TheRealFalseReality/aquapi/assets/STLModels/EZOCase/EZOBoard rev2.3mf

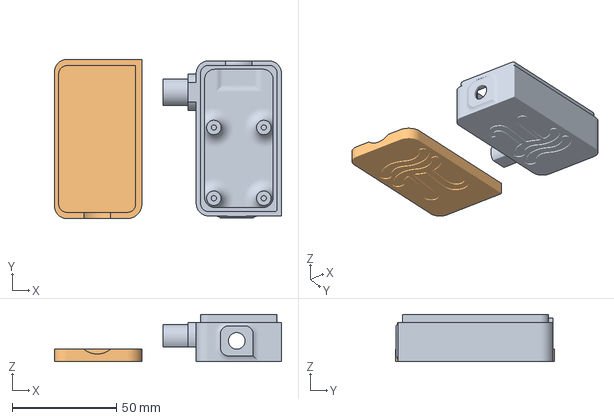
[picture p24: CAD file, 2026-02-03]
assets/STLModels/EZOCase/EZOBoard rev2.3mf
109.1 x 76.5 x 22.8 mm
EZOBoard Case rev2 v11.stl
EZOBoard Lid rev2 v14.stl
