TheRealFalseReality/aquapi/assets/STLModels/LeakSensor/Leak Sensor - Mag v13.stl

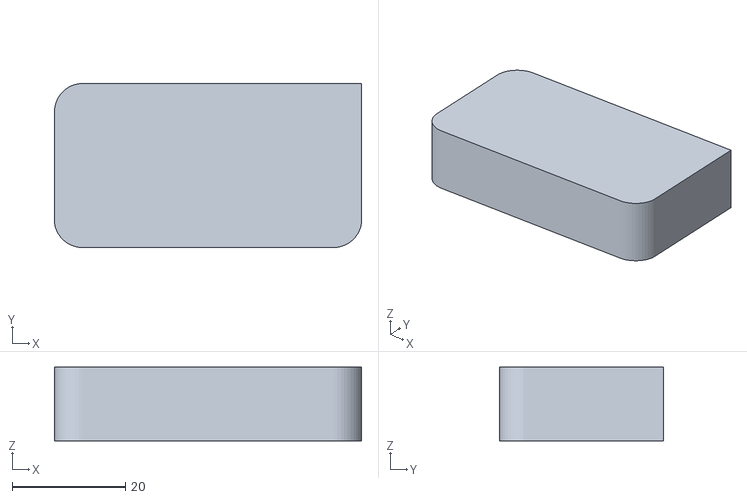
[picture p25: CAD file, 2025-01-13]
assets/STLModels/LeakSensor/Leak Sensor - Mag v13.stl
54.3 x 29.0 x 13.0
