TheRealFalseReality/aquapi/assets/STLModels/SnapCam/BallMount v9.stl

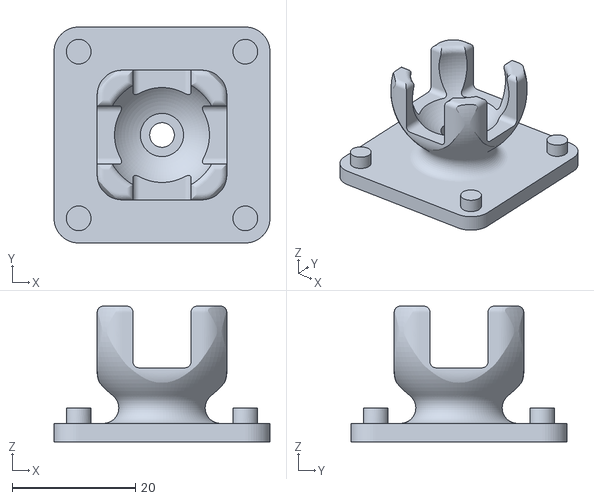
[picture p26: CAD file, 2024-07-31]
assets/STLModels/SnapCam/BallMount v9.stl
35.0 x 35.0 x 22.0
