TheRealFalseReality/aquapi/assets/STLModels/WaterLevelBracket/OpticalBracket_Holder.stl

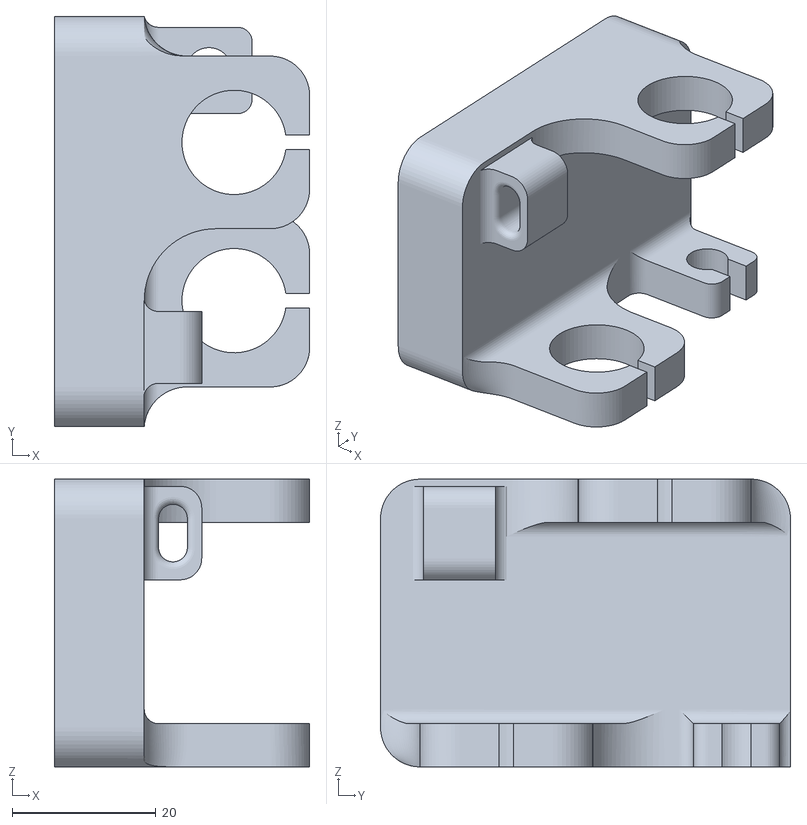
[picture p27: CAD file, 2026-02-03]
assets/STLModels/WaterLevelBracket/OpticalBracket_Holder.stl
35.5 x 57.0 x 40.0
