TheRealFalseReality/aquapi/assets/STLModels/AquaPiCase/AquaPi Case - Base v58.stl

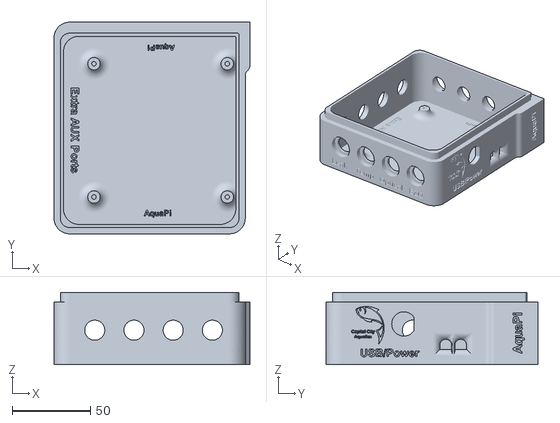
[picture p28: CAD file, 2026-02-03]
assets/STLModels/AquaPiCase/AquaPi Case - Base v58.stl
125.0 x 135.0 x 46.0
