TheRealFalseReality/aquapi/assets/STLModels/EZOPump/AquaPi Pump Lid - Red v26.stl

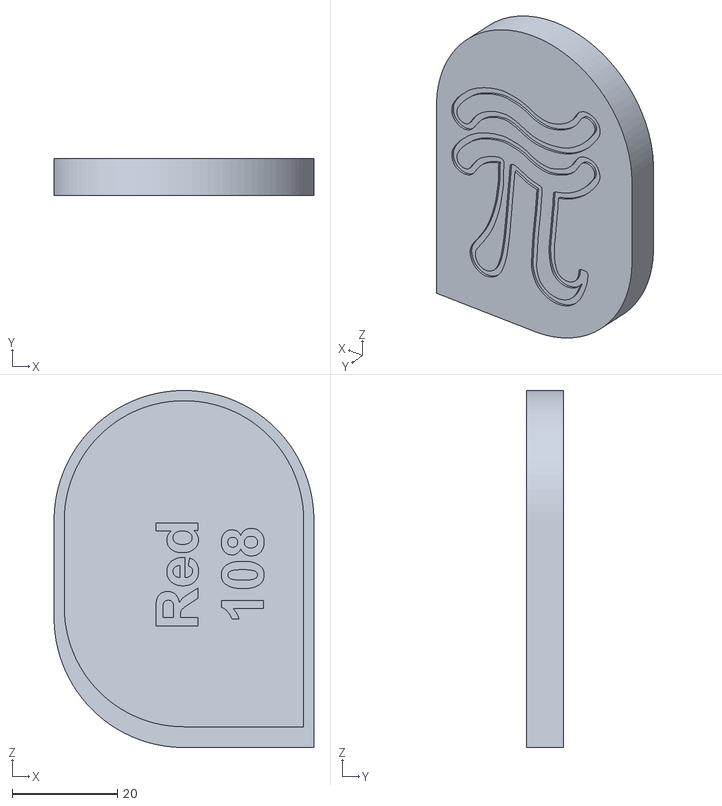
[picture p29: CAD file, 2026-02-03]
assets/STLModels/EZOPump/AquaPi Pump Lid - Red v26.stl
49.5 x 7.00 x 68.0
