TheRealFalseReality/aquapi/assets/STLModels/SnapCam/esp32Cam - Lid v32.stl

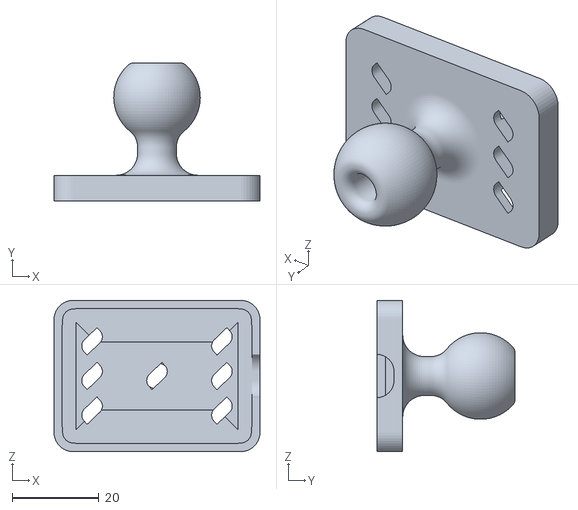
[picture p30: CAD file, 2024-07-31]
assets/STLModels/SnapCam/esp32Cam - Lid v32.stl
47.6 x 32.0 x 35.0
