TheRealFalseReality/aquapi/assets/STLModels/WaterLevelBracket/OpticalBracket Extender.stl

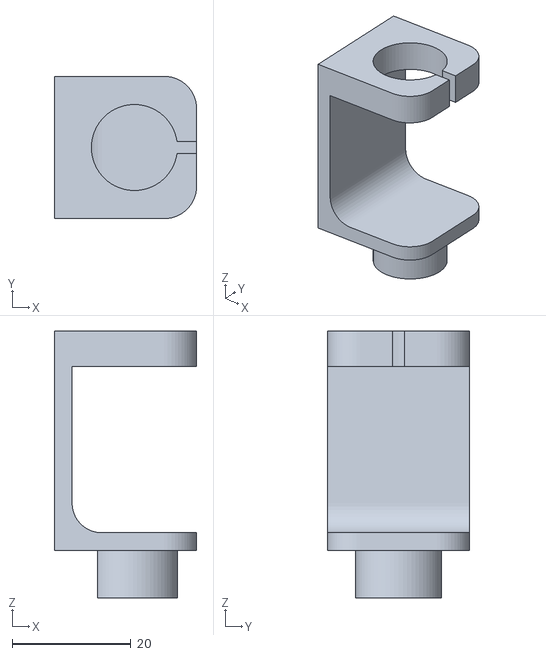
[picture p31: CAD file, 2025-01-13]
assets/STLModels/WaterLevelBracket/OpticalBracket Extender.stl
24.0 x 24.0 x 45.0
