TheRealFalseReality/aquapi/assets/STLModels/AquaPiCase/AquaPi Mount - Base v25.stl

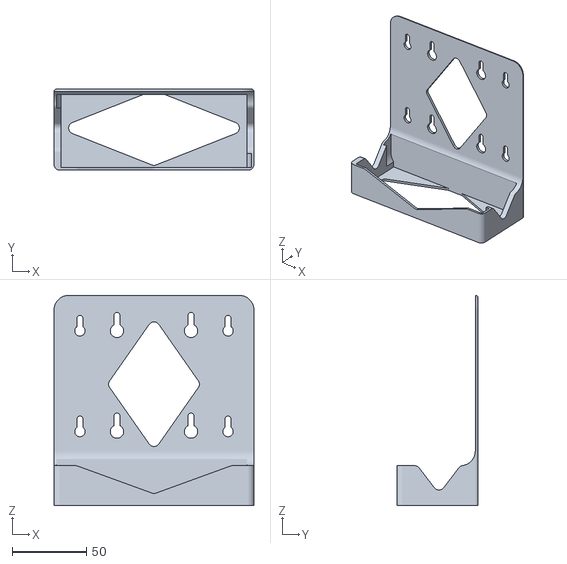
[picture p32: CAD file, 2024-11-28]
assets/STLModels/AquaPiCase/AquaPi Mount - Base v25.stl
135.0 x 55.0 x 142.0
