TheRealFalseReality/aquapi/assets/STLModels/AquaPiCase/AquaPi Mount - Hanger v25.stl

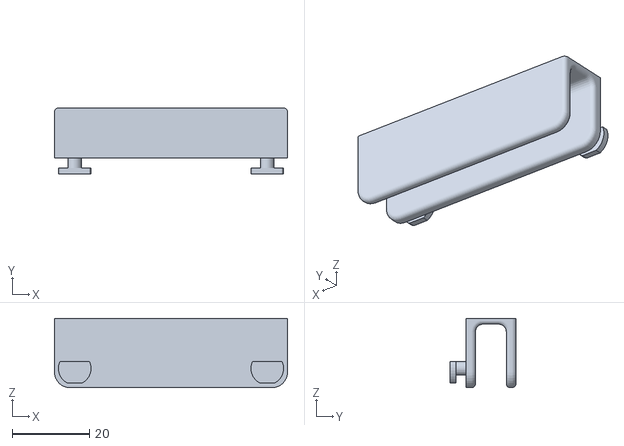
[picture p33: CAD file, 2024-11-28]
assets/STLModels/AquaPiCase/AquaPi Mount - Hanger v25.stl
60.5 x 17.1 x 18.0
