TheRealFalseReality/aquapi/assets/STLModels/AquaPiCase/AquaPi Case - Lid v45.stl

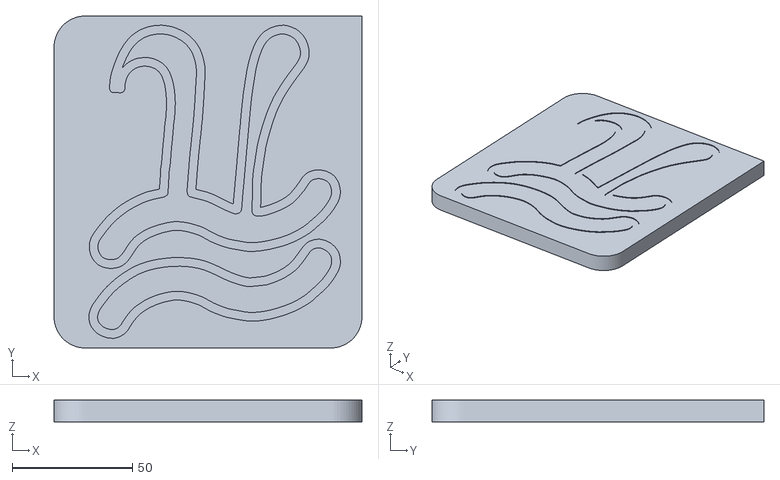
[picture p34: CAD file, 2024-07-30]
assets/STLModels/AquaPiCase/AquaPi Case - Lid v45.stl
128.0 x 138.0 x 9.00
