TheRealFalseReality/aquapi/common/ezo_pmp_duo.yaml

---
substitutions:
  # PMP circuit, who's address is 103
  addPMP_green: "109"  # Green - Clean
  addPMP_red: "108"  # Red - Waste #TODO Matches O2 sensor
  update_pmp_green: "60s"
  update_pmp_red: "60s"

  sorting_group_pump_green_weight: '81'
  sorting_group_pump_red_weight: '82'

web_server:
  sorting_groups:
    - id: sorting_group_pump_green
      name: "Pump - Green"
      sorting_weight: ${sorting_group_pump_green_weight}
    - id: sorting_group_pump_red
      name: "Pump - Red"
      sorting_weight: ${sorting_group_pump_red_weight}

ezo_pmp:
  - id: ezo_pump_green
    address: ${addPMP_green}
    update_interval: "${update_pmp_green}"
  - id: ezo_pump_red
    address: ${addPMP_red}
    update_interval: "${update_pmp_red}"

api:
  actions:
    - action: pump_waste_volume
      variables:
        dose_volume: float
      then:
        - ezo_pmp.dose_volume:
            id: ezo_pump_red
            volume: !lambda 'return dose_volume;'
    - action: pump_waste_volume_time
      variables:
        dose_volume: float
        dose_time: float
      then:
        - ezo_pmp.dose_volume_over_time:
            id: ezo_pump_red
            volume: !lambda |-
              return dose_volume;
            duration: !lambda |-
              return dose_time;
    - action: pump_waste_flow_rate_time
      variables:
        dose_rate: float
        dose_time: float
      then:
        - ezo_pmp.dose_with_constant_flow_rate:
            id: ezo_pump_red
            volume_per_minute: !lambda |-
              return dose_rate;
            duration: !lambda |-
              return dose_time;
    - action: pump_waste_set_calibration
      variables:
        actual_volume: float
      then:
        - ezo_pmp.set_calibration_volume:
            id: ezo_pump_red
            volume: !lambda |-
              return actual_volume;
    - action: pump_clean_volume
      variables:
        dose_volume: float
      then:
        - ezo_pmp.dose_volume:
            id: ezo_pump_green
            volume: !lambda 'return dose_volume;'
    - action: pump_clean_volume_time
      variables:
        dose_volume: float
        dose_time: float
      then:
        - ezo_pmp.dose_volume_over_time:
            id: ezo_pump_green
            volume: !lambda |-
              return dose_volume;
            duration: !lambda |-
              return dose_time;
    - action: pump_clean_flow_rate_time
      variables:
        dose_rate: float
        dose_time: float
      then:
        - ezo_pmp.dose_with_constant_flow_rate:
            id: ezo_pump_green
            volume_per_minute: !lambda |-
              return dose_rate;
            duration: !lambda |-
              return dose_time;
    - action: pump_clean_set_calibration
      variables:
        actual_volume: float
      then:
        - ezo_pmp.set_calibration_volume:
            id: ezo_pump_green
            volume: !lambda |-
              return actual_volume;
    - action: pump_water_change
      variables:
        volume: float
        duration: float
      then:
        - ezo_pmp.dose_volume_over_time:
            id: ezo_pump_green
            volume: !lambda |-
              return volume;
            duration: !lambda |-
              return duration;
        - ezo_pmp.dose_volume_over_time:
            id: ezo_pump_red
            volume: !lambda |-
              return volume;
            duration: !lambda |-
              return duration;
    - action: pump_water_change_quick
      variables:
        volume: float
      then:
        - ezo_pmp.dose_volume:
            id: ezo_pump_green
            volume: !lambda |-
              return volume;
        - ezo_pmp.dose_volume:
            id: ezo_pump_red
            volume: !lambda |-
              return volume;
    - action: pump_waste_change_address
      variables:
        address: int
      then:
        - ezo_pmp.change_i2c_address:
            id: ezo_pump_red
            address: !lambda |-
              return address;
    - action: pump_clean_change_address
      variables:
        address: int
      then:
        - ezo_pmp.change_i2c_address:
            id: ezo_pump_green
            address: !lambda |-
              return address;

sensor:
  # Green
  - platform: ezo_pmp
    id: ezo_pump_green
    current_volume_dosed:
      id: current_volume_dosed_clean
      name: Pump Clean - Current Volume Dosed
      disabled_by_default: true
      icon: mdi:cube-scan
      device_class: 'volume'
      state_class: total
      unit_of_measurement: 'mL'
      web_server:
        sorting_group_id: sorting_group_pump_green
  - platform: ezo_pmp
    id: ezo_pump_green
    total_volume_dosed:
      id: total_volume_dosed_clean
      name: Pump Clean - Total Volume Dosed
      icon: mdi:timer-sand-empty
      disabled_by_default: true
      device_class: 'volume'
      unit_of_measurement: 'mL'
      web_server:
        sorting_group_id: sorting_group_pump_green
  - platform: ezo_pmp
    id: ezo_pump_green
    absolute_total_volume_dosed:
      id: absolute_total_volume_dosed_clean
      name: Pump Clean - Absolute Total Volume Dosed
      icon: mdi:timer-sand-full
      device_class: 'volume'
      state_class: total
      unit_of_measurement: 'mL'
      disabled_by_default: true
      web_server:
        sorting_group_id: sorting_group_pump_green
  - platform: ezo_pmp
    id: ezo_pump_green
    last_volume_requested:
      id: last_volume_requested_clean
      name: Pump Clean - Last Volume Requested
      icon: mdi:history
      device_class: 'volume'
      state_class: total
      unit_of_measurement: 'mL'
      disabled_by_default: true
      web_server:
        sorting_group_id: sorting_group_pump_green
  - platform: ezo_pmp
    id: ezo_pump_green
    max_flow_rate:
      id: max_flow_rate_clean
      name: Pump Clean - Max Volume-Time Flow Rate
      icon: mdi:car-speed-limiter
      unit_of_measurement: 'mL/min'
      disabled_by_default: true
      web_server:
        sorting_group_id: sorting_group_pump_green
  - platform: ezo_pmp
    id: ezo_pump_green
    pump_voltage:
      id: pump_voltage_clean
      name: Pump Clean - Voltage
      icon: mdi:lightning-bolt-circle
      disabled_by_default: true
      device_class: 'voltage'
      web_server:
        sorting_group_id: sorting_group_pump_green

  # Red
  - platform: ezo_pmp
    id: ezo_pump_red
    current_volume_dosed:
      id: current_volume_dosed_waste
      name: Pump Waste - Current Volume Dosed
      disabled_by_default: true
      icon: mdi:cube-scan
      device_class: 'volume'
      state_class: total
      unit_of_measurement: 'mL'
      web_server:
        sorting_group_id: sorting_group_pump_red
  - platform: ezo_pmp
    id: ezo_pump_red
    total_volume_dosed:
      id: total_volume_dosed_waste
      name: Pump Waste - Total Volume Dosed
      icon: mdi:timer-sand-empty
      device_class: 'volume'
      unit_of_measurement: 'mL'
      disabled_by_default: true
      web_server:
        sorting_group_id: sorting_group_pump_red
  - platform: ezo_pmp
    id: ezo_pump_red
    absolute_total_volume_dosed:
      id: absolute_total_volume_dosed_waste
      name: Pump Waste - Absolute Total Volume Dosed
      icon: mdi:timer-sand-full
      device_class: 'volume'
      state_class: total
      disabled_by_default: true
      unit_of_measurement: 'mL'
      web_server:
        sorting_group_id: sorting_group_pump_red
  - platform: ezo_pmp
    id: ezo_pump_red
    last_volume_requested:
      id: last_volume_requested_waste
      name: Pump Waste - Last Volume Requested
      icon: mdi:history
      state_class: total
      device_class: 'volume'
      unit_of_measurement: 'mL'
      disabled_by_default: true
      web_server:
        sorting_group_id: sorting_group_pump_red
  - platform: ezo_pmp
    id: ezo_pump_red
    max_flow_rate:
      id: max_flow_rate_waste
      name: Pump Waste - Max Volume-Time Flow Rate
      icon: mdi:car-speed-limiter
      unit_of_measurement: 'mL/min'
      disabled_by_default: true
      web_server:
        sorting_group_id: sorting_group_pump_red
  - platform: ezo_pmp
    id: ezo_pump_red
    pump_voltage:
      id: pump_voltage_waste
      name: Pump Waste - Voltage
      icon: mdi:lightning-bolt-circle
      disabled_by_default: true
      device_class: 'voltage'
      web_server:
        sorting_group_id: sorting_group_pump_red

binary_sensor:
  # Green
  - platform: ezo_pmp
    id: ezo_pump_green
    pump_state:
      id: pump_state_clean
      icon: mdi:pump
      name: Pump Clean - State
      disabled_by_default: true
      web_server:
        sorting_group_id: sorting_group_pump_green
  - platform: ezo_pmp
    id: ezo_pump_green
    is_paused:
      id: is_paused_clean
      name: Pump Clean - Paused Status
      icon: mdi:pause
      disabled_by_default: true
      web_server:
        sorting_group_id: sorting_group_pump_green

  # Red
  - platform: ezo_pmp
    id: ezo_pump_red
    pump_state:
      id: pump_state_waste
      icon: mdi:pump
      name: Pump Waste - State
      disabled_by_default: true
      web_server:
        sorting_group_id: sorting_group_pump_red
  - platform: ezo_pmp
    id: ezo_pump_red
    is_paused:
      id: is_paused_waste
      name: Pump Waste - Paused Status
      icon: mdi:pause
      disabled_by_default: true
      web_server:
        sorting_group_id: sorting_group_pump_red

text_sensor:
  # Green
  - platform: ezo_pmp
    id: ezo_pump_green
    dosing_mode:
      id: dosing_mode_clean
      name: Pump Clean - Dosing Mode
      disabled_by_default: true
      icon: mdi:auto-mode
      web_server:
        sorting_group_id: sorting_group_pump_green
  - platform: ezo_pmp
    id: ezo_pump_green
    calibration_status:
      id: calibration_status_clean
      name: Pump Clean - Calibration Status
      disabled_by_default: true
      icon: mdi:tape-measure
      web_server:
        sorting_group_id: sorting_group_pump_green

  # Red
  - platform: ezo_pmp
    id: ezo_pump_red
    dosing_mode:
      id: dosing_mode_waste
      name: Pump Waste - Dosing Mode
      disabled_by_default: true
      icon: mdi:auto-mode
      web_server:
        sorting_group_id: sorting_group_pump_red
  - platform: ezo_pmp
    id: ezo_pump_red
    calibration_status:
      id: calibration_status_waste
      name: Pump Waste - Calibration Status
      disabled_by_default: true
      icon: mdi:tape-measure
      web_server:
        sorting_group_id: sorting_group_pump_red

number:
  # Green
  - platform: template
    id: volume_clean
    icon: mdi:pump
    name: Pump Clean - Volume to Dose (negative = reverse)
    disabled_by_default: true
    device_class: 'volume'
    unit_of_measurement: 'mL'
    optimistic: true
    initial_value: 10  # cannot be less than +/-0.1mL
    min_value: -378541  # Negative values run pump in reverse direction
    max_value: 378541   # 100 gal in mL
    mode: box
    step: 0.1
    web_server:
      sorting_group_id: sorting_group_pump_green
  - platform: template
    id: duration_clean
    icon: mdi:timer
    name: Pump Clean - Time to Dose
    disabled_by_default: true
    device_class: 'duration'
    unit_of_measurement: 'min'
    optimistic: true
    initial_value: 1
    min_value: 1
    max_value: 1440  # 24 hours
    mode: box
    step: 0.1
    web_server:
      sorting_group_id: sorting_group_pump_green
  - platform: template
    id: flow_rate_clean
    icon: mdi:waves-arrow-right
    name: Pump Clean - Volume-Time Flow Rate
    disabled_by_default: true
    unit_of_measurement: 'mL/min'
    optimistic: true
    initial_value: 10
    min_value: .5
    max_value: 105  # may need to lower to 40
    mode: box
    step: 0.1
    web_server:
      sorting_group_id: sorting_group_pump_green

  # Red
  - platform: template
    id: volume_waste
    icon: mdi:pump
    name: Pump Waste - Volume to Dose (negative = reverse)
    disabled_by_default: true
    device_class: 'volume'
    unit_of_measurement: 'mL'
    optimistic: true
    initial_value: 10  # cannot be less than +/-0.1mL
    min_value: -378541  # Negative values run pump in reverse direction
    max_value: 378541   # 100 gal in mL
    mode: box
    step: 0.1
    web_server:
      sorting_group_id: sorting_group_pump_red
  - platform: template
    id: duration_waste
    icon: mdi:timer
    name: Pump Waste - Time to Dose
    disabled_by_default: true
    device_class: 'duration'
    unit_of_measurement: 'min'
    optimistic: true
    initial_value: 1
    min_value: 1
    max_value: 1440  # 24 hours
    mode: box
    step: 0.1
    web_server:
      sorting_group_id: sorting_group_pump_red
  - platform: template
    id: flow_rate_waste
    icon: mdi:waves-arrow-left
    name: Pump Waste - Volume-Time Flow Rate
    disabled_by_default: true
    unit_of_measurement: 'mL/min'
    optimistic: true
    initial_value: 10
    min_value: .5
    max_value: 105  # may need to lower to 40
    mode: box
    step: 0.1
    web_server:
      sorting_group_id: sorting_group_pump_red

button:
  # Green
  - platform: template
    name: Pump Clean - Dose Volume for Time
    disabled_by_default: true
    icon: mdi:clock-time-two-outline
    id: dose_over_time_clean
    on_press:
      - ezo_pmp.dose_volume_over_time:
          id: ezo_pump_green
          volume: !lambda |-
            return id(volume_clean).state;
          duration: !lambda |-
            return id(duration_clean).state;
    web_server:
      sorting_group_id: sorting_group_pump_green
  - platform: template
    name: Pump Clean - Dose Continuously
    disabled_by_default: true
    icon: mdi:infinity
    id: dose_continuously_clean
    on_press:
      - ezo_pmp.dose_continuously:
          id: ezo_pump_green
    web_server:
      sorting_group_id: sorting_group_pump_green
  - platform: template
    name: Pump Clean - Dose Volume (negative = reverse)
    disabled_by_default: true
    icon: mdi:pump
    id: dose_volume_clean
    on_press:
      - ezo_pmp.dose_volume:
          id: ezo_pump_green
          volume: !lambda |-
            return id(volume_clean).state;
    web_server:
      sorting_group_id: sorting_group_pump_green
  - platform: template
    name: Pump Clean - Dose at Volume-Time Flow Rate for Time
    disabled_by_default: true
    icon: mdi:format-text-wrapping-overflow
    id: dose_flow_rate_clean
    on_press:
      - ezo_pmp.dose_with_constant_flow_rate:
          id: ezo_pump_green
          volume_per_minute: !lambda |-
            return id(flow_rate_clean).state;
          duration: !lambda |-
            return id(duration_clean).state;
    web_server:
      sorting_group_id: sorting_group_pump_green
  - platform: template
    name: Pump Clean - Pause Dosing
    disabled_by_default: true
    icon: mdi:pause
    id: dose_pause_clean
    on_press:
      - ezo_pmp.pause_dosing:
          id: ezo_pump_green
    web_server:
      sorting_group_id: sorting_group_pump_green
  - platform: template
    name: Pump Clean - Stop Dosing
    disabled_by_default: true
    icon: mdi:stop
    id: dose_stop_clean
    on_press:
      - ezo_pmp.stop_dosing:
          id: ezo_pump_green
    web_server:
      sorting_group_id: sorting_group_pump_green
  - platform: template
    name: Pump Clean - Clear Total Volume Dosed
    disabled_by_default: true
    icon: mdi:backspace
    id: dose_clear_clean
    on_press:
      - ezo_pmp.clear_total_volume_dosed:
          id: ezo_pump_green
    web_server:
      sorting_group_id: sorting_group_pump_green
  - platform: template
    name: Pump Clean - Set Calibration Volume
    disabled_by_default: true
    icon: mdi:tape-measure
    id: dose_calibrate_volume_clean
    on_press:
      - ezo_pmp.set_calibration_volume:
          id: ezo_pump_green
          volume: !lambda |-
            return id(volume_clean).state;
    web_server:
      sorting_group_id: sorting_group_pump_green
  - platform: template
    name: Pump Clean - Clear Calibration Volume
    icon: mdi:cancel
    id: dose_calibrate_volume_clear_clean
    disabled_by_default: true
    on_press:
      - ezo_pmp.clear_calibration:
          id: ezo_pump_green
    web_server:
      sorting_group_id: sorting_group_pump_green

  # Red
  - platform: template
    name: Pump Waste - Dose Volume for Time
    disabled_by_default: true
    icon: mdi:clock-time-two-outline
    id: dose_over_time_waste
    on_press:
      - ezo_pmp.dose_volume_over_time:
          id: ezo_pump_red
          volume: !lambda |-
            return id(volume_waste).state;
          duration: !lambda |-
            return id(duration_waste).state;
    web_server:
      sorting_group_id: sorting_group_pump_red
  - platform: template
    name: Pump Waste - Dose Continuously
    disabled_by_default: true
    icon: mdi:infinity
    id: dose_continuously_waste
    on_press:
      - ezo_pmp.dose_continuously:
          id: ezo_pump_red
    web_server:
      sorting_group_id: sorting_group_pump_red
  - platform: template
    name: Pump Waste - Dose Volume (negative = reverse)
    disabled_by_default: true
    icon: mdi:pump
    id: dose_volume_waste
    on_press:
      - ezo_pmp.dose_volume:
          id: ezo_pump_red
          volume: !lambda |-
            return id(volume_waste).state;
    web_server:
      sorting_group_id: sorting_group_pump_red
  - platform: template
    name: Pump Waste - Dose at Volume-Time Flow Rate for Time
    disabled_by_default: true
    icon: mdi:format-text-wrapping-overflow
    id: dose_flow_rate_waste
    on_press:
      - ezo_pmp.dose_with_constant_flow_rate:
          id: ezo_pump_red
          volume_per_minute: !lambda |-
            return id(flow_rate_waste).state;
          duration: !lambda |-
            return id(duration_waste).state;
    web_server:
      sorting_group_id: sorting_group_pump_red
  - platform: template
    name: Pump Waste - Pause Dosing
    disabled_by_default: true
    icon: mdi:pause
    id: dose_pause_waste
    on_press:
      - ezo_pmp.pause_dosing:
          id: ezo_pump_red
    web_server:
      sorting_group_id: sorting_group_pump_red
  - platform: template
    name: Pump Waste - Stop Dosing
    disabled_by_default: true
    icon: mdi:stop
    id: dose_stop_waste
    on_press:
      - ezo_pmp.stop_dosing:
          id: ezo_pump_red
    web_server:
      sorting_group_id: sorting_group_pump_red
  - platform: template
    name: Pump Waste - Clear Total Volume Dosed
    icon: mdi:backspace
    disabled_by_default: true
    id: dose_clear_waste
    on_press:
      - ezo_pmp.clear_total_volume_dosed:
          id: ezo_pump_red
    web_server:
      sorting_group_id: sorting_group_pump_red
  - platform: template
    name: Pump Waste - Set Calibration Volume
    disabled_by_default: true
    icon: mdi:tape-measure
    id: dose_calibrate_volume_waste
    on_press:
      - ezo_pmp.set_calibration_volume:
          id: ezo_pump_red
          volume: !lambda |-
            return id(volume_waste).state;
    web_server:
      sorting_group_id: sorting_group_pump_red
  - platform: template
    name: Pump Waste - Clear Calibration Volume
    disabled_by_default: true
    icon: mdi:cancel
    id: dose_calibrate_volume_clear_waste
    on_press:
      - ezo_pmp.clear_calibration:
          id: ezo_pump_red
    web_server:
      sorting_group_id: sorting_group_pump_red
