TheRealFalseReality/aquapi/common/ezo_pmp_blue.yaml

---
substitutions:
  # PMP circuit
  addPMP_blue: "106"  # blue
  update_pmp_blue: "60s"
  sorting_group_pump_blue_weight: '83'

web_server:
  sorting_groups:
    - id: sorting_group_pump_blue
      name: "Pump - Blue"
      sorting_weight: ${sorting_group_pump_blue_weight}

ezo_pmp:
  - id: ezo_pump_blue
    address: ${addPMP_blue}
    update_interval: "${update_pmp_blue}"

api:
  actions:
    - action: pump_blue_dose_volume
      variables:
        dose_volume: float
      then:
        - ezo_pmp.dose_volume:
            id: ezo_pump_blue
            volume: !lambda 'return dose_volume;'
    - action: pump_blue_dose_volume_time
      variables:
        dose_volume: float
        dose_time: float
      then:
        - ezo_pmp.dose_volume_over_time:
            id: ezo_pump_blue
            volume: !lambda |-
              return dose_volume;
            duration: !lambda |-
              return dose_time;
    - action: pump_blue_dose_flow_rate_time
      variables:
        dose_rate: float
        dose_time: float
      then:
        - ezo_pmp.dose_with_constant_flow_rate:
            id: ezo_pump_blue
            volume_per_minute: !lambda |-
              return dose_rate;
            duration: !lambda |-
              return dose_time;
    - action: pump_blue_dose_set_calibration
      variables:
        actual_volume: float
      then:
        - ezo_pmp.set_calibration_volume:
            id: ezo_pump_blue
            volume: !lambda |-
              return actual_volume;
    - action: pump_blue_change_address
      variables:
        address: int
      then:
        - ezo_pmp.change_i2c_address:
            id: ezo_pump_blue
            address: !lambda |-
              return address;

sensor:
  - platform: ezo_pmp
    id: ezo_pump_blue
    current_volume_dosed:
      id: current_volume_dosed_blue
      name: Pump Blue - Current Volume Dosed
      icon: mdi:cube-scan
      device_class: 'volume'
      state_class: total
      unit_of_measurement: 'mL'
      web_server:
        sorting_group_id: sorting_group_pump_blue
  - platform: ezo_pmp
    id: ezo_pump_blue
    total_volume_dosed:
      id: total_volume_dosed_blue
      name: Pump Blue - Total Volume Dosed
      icon: mdi:timer-sand-empty
      device_class: 'volume'
      unit_of_measurement: 'mL'
      disabled_by_default: true
      web_server:
        sorting_group_id: sorting_group_pump_blue
  - platform: ezo_pmp
    id: ezo_pump_blue
    absolute_total_volume_dosed:
      id: absolute_total_volume_dosed_blue
      name: Pump Blue - Absolute Total Volume Dosed
      icon: mdi:timer-sand-full
      disabled_by_default: true
      device_class: 'volume'
      state_class: total
      unit_of_measurement: 'mL'
      web_server:
        sorting_group_id: sorting_group_pump_blue
  - platform: ezo_pmp
    id: ezo_pump_blue
    last_volume_requested:
      id: last_volume_requested_blue
      name: Pump Blue - Last Volume Requested
      icon: mdi:history
      device_class: 'volume'
      disabled_by_default: true
      state_class: total
      unit_of_measurement: 'mL'
      web_server:
        sorting_group_id: sorting_group_pump_blue
  - platform: ezo_pmp
    id: ezo_pump_blue
    max_flow_rate:
      id: max_flow_rate_blue
      name: Pump Blue - Max Volume-Time Flow Rate
      icon: mdi:car-speed-limiter
      disabled_by_default: true
      unit_of_measurement: 'mL/min'
      web_server:
        sorting_group_id: sorting_group_pump_blue
  - platform: ezo_pmp
    id: ezo_pump_blue
    pump_voltage:
      id: pump_blue_voltage
      name: Pump Blue - Voltage
      disabled_by_default: true
      icon: mdi:lightning-bolt-circle
      device_class: 'voltage'
      web_server:
        sorting_group_id: sorting_group_pump_blue

binary_sensor:
  - platform: ezo_pmp
    id: ezo_pump_blue
    pump_state:
      id: pump_blue_state
      name: Pump Blue - State
      icon: mdi:pump_blue
  - platform: ezo_pmp
    id: ezo_pump_blue
    is_paused:
      id: is_paused_blue
      name: Pump Blue - Paused Status
      icon: mdi:pause
      disabled_by_default: true
      web_server:
        sorting_group_id: sorting_group_pump_blue

text_sensor:
  - platform: ezo_pmp
    id: ezo_pump_blue
    dosing_mode:
      id: dosing_mode_blue
      name: Pump Blue - Dosing Mode
      icon: mdi:auto-mode
      web_server:
        sorting_group_id: sorting_group_pump_blue
  - platform: ezo_pmp
    id: ezo_pump_blue
    calibration_status:
      id: calibration_status_blue
      name: Pump Blue - Calibration Status
      disabled_by_default: true
      icon: mdi:tape-measure
      web_server:
        sorting_group_id: sorting_group_pump_blue

number:
  - platform: template
    id: volume_blue
    icon: mdi:pump_blue
    name: Pump Blue - Volume to Dose (negative = reverse)
    device_class: 'volume'
    unit_of_measurement: 'mL'
    optimistic: true
    initial_value: 10  # cannot be less than +/-0.1mL
    min_value: -378541  # Negative values run pump in reverse direction
    max_value: 378541   # 100 gal in mL
    mode: box
    step: 0.1
    web_server:
      sorting_group_id: sorting_group_pump_blue
  - platform: template
    id: duration_blue
    icon: mdi:timer
    name: Pump Blue - Time to Dose
    device_class: 'duration'
    unit_of_measurement: 'min'
    optimistic: true
    initial_value: 1
    min_value: 1
    max_value: 1440  # 24 hours
    mode: box
    step: 0.1
    web_server:
      sorting_group_id: sorting_group_pump_blue
  - platform: template
    id: flow_rate_blue
    icon: mdi:waves-arrow-right
    name: Pump Blue - Volume-Time Flow Rate
    unit_of_measurement: 'mL/min'
    optimistic: true
    initial_value: 10
    min_value: .5
    max_value: 105  # may need to lower to 40
    mode: box
    step: 0.1
    web_server:
      sorting_group_id: sorting_group_pump_blue

button:
  - platform: template
    name: Pump Blue - Dose Volume for Time
    icon: mdi:clock-time-two-outline
    id: dose_over_time_blue
    on_press:
      - ezo_pmp.dose_volume_over_time:
          id: ezo_pump_blue
          volume: !lambda |-
            return id(volume_blue).state;
          duration: !lambda |-
            return id(volume_blue).state;
    web_server:
      sorting_group_id: sorting_group_pump_blue
  - platform: template
    name: Pump Blue - Dose Continuously
    icon: mdi:infinity
    id: dose_continuously_blue
    on_press:
      - ezo_pmp.dose_continuously:
          id: ezo_pump_blue
    web_server:
      sorting_group_id: sorting_group_pump_blue
  - platform: template
    name: Pump Blue - Dose Volume (negative = reverse)
    icon: mdi:pump_blue
    id: dose_volume_blue
    on_press:
      - ezo_pmp.dose_volume:
          id: ezo_pump_blue
          volume: !lambda |-
            return id(volume_blue).state;
    web_server:
      sorting_group_id: sorting_group_pump_blue
  - platform: template
    name: Pump Blue - Dose at Volume-Time Flow Rate for Time
    icon: mdi:format-text-wrapping-overflow
    id: dose_flow_rate_blue
    on_press:
      - ezo_pmp.dose_with_constant_flow_rate:
          id: ezo_pump_blue
          volume_per_minute: !lambda |-
            return id(volume_blue).state;
          duration: !lambda |-
            return id(volume_blue).state;
    web_server:
      sorting_group_id: sorting_group_pump_blue
  - platform: template
    name: Pump Blue - Pause Dosing
    icon: mdi:pause
    id: dose_pause_blue
    on_press:
      - ezo_pmp.pause_dosing:
          id: ezo_pump_blue
    web_server:
      sorting_group_id: sorting_group_pump_blue
  - platform: template
    name: Pump Blue - Stop Dosing
    icon: mdi:stop
    id: dose_stop_blue
    on_press:
      - ezo_pmp.stop_dosing:
          id: ezo_pump_blue
    web_server:
      sorting_group_id: sorting_group_pump_blue
  - platform: template
    name: Pump Blue - Clear Total Volume Dosed
    disabled_by_default: true
    icon: mdi:backspace
    id: dose_clear_blue
    on_press:
      - ezo_pmp.clear_total_volume_dosed:
          id: ezo_pump_blue
    web_server:
      sorting_group_id: sorting_group_pump_blue

  # Calibrate
  - platform: template
    name: Pump Blue - Set Calibration Volume
    icon: mdi:tape-measure
    id: dose_calibrate_volume_blue
    on_press:
      - ezo_pmp.set_calibration_volume:
          id: ezo_pump_blue
          volume: !lambda |-
            return id(volume_blue).state;
    web_server:
      sorting_group_id: sorting_group_pump_blue
  - platform: template
    name: Pump Blue - Clear Calibration Volume
    disabled_by_default: true
    icon: mdi:cancel
    id: dose_calibrate_volume_clear_blue
    on_press:
      - ezo_pmp.clear_calibration:
          id: ezo_pump_blue
    web_server:
      sorting_group_id: sorting_group_pump_blue
