TheRealFalseReality/aquapi/common/ezo_pmp_yellow.yaml

---
substitutions:
  # PMP circuit
  addPMP_yellow: "104"  # Yellow
  update_pmp_yellow: "60s"
  sorting_group_pump_yellow_weight: '85'

web_server:
  sorting_groups:
    - id: sorting_group_pump_yellow
      name: "Pump - Yellow"
      sorting_weight: ${sorting_group_pump_yellow_weight}

ezo_pmp:
  - id: ezo_pump_yellow
    address: ${addPMP_yellow}
    update_interval: "${update_pmp_yellow}"

api:
  actions:
    - action: pump_yellow_dose_volume
      variables:
        dose_volume: float
      then:
        - ezo_pmp.dose_volume:
            id: ezo_pump_yellow
            volume: !lambda 'return dose_volume;'
    - action: pump_yellow_dose_volume_time
      variables:
        dose_volume: float
        dose_time: float
      then:
        - ezo_pmp.dose_volume_over_time:
            id: ezo_pump_yellow
            volume: !lambda |-
              return dose_volume;
            duration: !lambda |-
              return dose_time;
    - action: pump_yellow_dose_flow_rate_time
      variables:
        dose_rate: float
        dose_time: float
      then:
        - ezo_pmp.dose_with_constant_flow_rate:
            id: ezo_pump_yellow
            volume_per_minute: !lambda |-
              return dose_rate;
            duration: !lambda |-
              return dose_time;
    - action: pump_yellow_dose_set_calibration
      variables:
        actual_volume: float
      then:
        - ezo_pmp.set_calibration_volume:
            id: ezo_pump_yellow
            volume: !lambda |-
              return actual_volume;
    - action: pump_yellow_change_address
      variables:
        address: int
      then:
        - ezo_pmp.change_i2c_address:
            id: ezo_pump_yellow
            address: !lambda |-
              return address;

sensor:
  - platform: ezo_pmp
    id: ezo_pump_yellow
    current_volume_dosed:
      id: current_volume_dosed_yellow
      name: Pump Yellow - Current Volume Dosed
      icon: mdi:cube-scan
      device_class: 'volume'
      state_class: total
      unit_of_measurement: 'mL'
      web_server:
        sorting_group_id: sorting_group_pump_yellow
  - platform: ezo_pmp
    id: ezo_pump_yellow
    total_volume_dosed:
      id: total_volume_dosed_yellow
      name: Pump Yellow - Total Volume Dosed
      icon: mdi:timer-sand-empty
      device_class: 'volume'
      unit_of_measurement: 'mL'
      disabled_by_default: true
      web_server:
        sorting_group_id: sorting_group_pump_yellow
  - platform: ezo_pmp
    id: ezo_pump_yellow
    absolute_total_volume_dosed:
      id: absolute_total_volume_dosed_yellow
      name: Pump Yellow - Absolute Total Volume Dosed
      icon: mdi:timer-sand-full
      disabled_by_default: true
      device_class: 'volume'
      state_class: total
      unit_of_measurement: 'mL'
      web_server:
        sorting_group_id: sorting_group_pump_yellow
  - platform: ezo_pmp
    id: ezo_pump_yellow
    last_volume_requested:
      id: last_volume_requested_yellow
      name: Pump Yellow - Last Volume Requested
      icon: mdi:history
      device_class: 'volume'
      disabled_by_default: true
      state_class: total
      unit_of_measurement: 'mL'
      web_server:
        sorting_group_id: sorting_group_pump_yellow
  - platform: ezo_pmp
    id: ezo_pump_yellow
    max_flow_rate:
      id: max_flow_rate_yellow
      name: Pump Yellow - Max Volume-Time Flow Rate
      icon: mdi:car-speed-limiter
      disabled_by_default: true
      unit_of_measurement: 'mL/min'
      web_server:
        sorting_group_id: sorting_group_pump_yellow
  - platform: ezo_pmp
    id: ezo_pump_yellow
    pump_voltage:
      id: pump_yellow_voltage
      name: Pump Yellow - Voltage
      disabled_by_default: true
      icon: mdi:lightning-bolt-circle
      device_class: 'voltage'
      web_server:
        sorting_group_id: sorting_group_pump_yellow

binary_sensor:
  - platform: ezo_pmp
    id: ezo_pump_yellow
    pump_state:
      id: pump_yellow_state
      name: Pump Yellow - State
      icon: mdi:pump_yellow
  - platform: ezo_pmp
    id: ezo_pump_yellow
    is_paused:
      id: is_paused_yellow
      name: Pump Yellow - Paused Status
      icon: mdi:pause
      disabled_by_default: true
      web_server:
        sorting_group_id: sorting_group_pump_yellow

text_sensor:
  - platform: ezo_pmp
    id: ezo_pump_yellow
    dosing_mode:
      id: dosing_mode_yellow
      name: Pump Yellow - Dosing Mode
      icon: mdi:auto-mode
      web_server:
        sorting_group_id: sorting_group_pump_yellow
  - platform: ezo_pmp
    id: ezo_pump_yellow
    calibration_status:
      id: calibration_status_yellow
      name: Pump Yellow - Calibration Status
      disabled_by_default: true
      icon: mdi:tape-measure
      web_server:
        sorting_group_id: sorting_group_pump_yellow

number:
  - platform: template
    id: volume_yellow
    icon: mdi:pump_yellow
    name: Pump Yellow - Volume to Dose (negative = reverse)
    device_class: 'volume'
    unit_of_measurement: 'mL'
    optimistic: true
    initial_value: 10  # cannot be less than +/-0.1mL
    min_value: -378541  # Negative values run pump in reverse direction
    max_value: 378541   # 100 gal in mL
    mode: box
    step: 0.1
    web_server:
      sorting_group_id: sorting_group_pump_yellow
  - platform: template
    id: duration_yellow
    icon: mdi:timer
    name: Pump Yellow - Time to Dose
    device_class: 'duration'
    unit_of_measurement: 'min'
    optimistic: true
    initial_value: 1
    min_value: 1
    max_value: 1440  # 24 hours
    mode: box
    step: 0.1
    web_server:
      sorting_group_id: sorting_group_pump_yellow
  - platform: template
    id: flow_rate_yellow
    icon: mdi:waves-arrow-right
    name: Pump Yellow - Volume-Time Flow Rate
    unit_of_measurement: 'mL/min'
    optimistic: true
    initial_value: 10
    min_value: .5
    max_value: 105  # may need to lower to 40
    mode: box
    step: 0.1
    web_server:
      sorting_group_id: sorting_group_pump_yellow

button:
  - platform: template
    name: Pump Yellow - Dose Volume for Time
    icon: mdi:clock-time-two-outline
    id: dose_over_time_yellow
    on_press:
      - ezo_pmp.dose_volume_over_time:
          id: ezo_pump_yellow
          volume: !lambda |-
            return id(volume_yellow).state;
          duration: !lambda |-
            return id(volume_yellow).state;
    web_server:
      sorting_group_id: sorting_group_pump_yellow
  - platform: template
    name: Pump Yellow - Dose Continuously
    icon: mdi:infinity
    id: dose_continuously_yellow
    on_press:
      - ezo_pmp.dose_continuously:
          id: ezo_pump_yellow
    web_server:
      sorting_group_id: sorting_group_pump_yellow
  - platform: template
    name: Pump Yellow - Dose Volume (negative = reverse)
    icon: mdi:pump_yellow
    id: dose_volume_yellow
    on_press:
      - ezo_pmp.dose_volume:
          id: ezo_pump_yellow
          volume: !lambda |-
            return id(volume_yellow).state;
    web_server:
      sorting_group_id: sorting_group_pump_yellow
  - platform: template
    name: Pump Yellow - Dose at Volume-Time Flow Rate for Time
    icon: mdi:format-text-wrapping-overflow
    id: dose_flow_rate_yellow
    on_press:
      - ezo_pmp.dose_with_constant_flow_rate:
          id: ezo_pump_yellow
          volume_per_minute: !lambda |-
            return id(volume_yellow).state;
          duration: !lambda |-
            return id(volume_yellow).state;
    web_server:
      sorting_group_id: sorting_group_pump_yellow
  - platform: template
    name: Pump Yellow - Pause Dosing
    icon: mdi:pause
    id: dose_pause_yellow
    on_press:
      - ezo_pmp.pause_dosing:
          id: ezo_pump_yellow
    web_server:
      sorting_group_id: sorting_group_pump_yellow
  - platform: template
    name: Pump Yellow - Stop Dosing
    icon: mdi:stop
    id: dose_stop_yellow
    on_press:
      - ezo_pmp.stop_dosing:
          id: ezo_pump_yellow
    web_server:
      sorting_group_id: sorting_group_pump_yellow
  - platform: template
    name: Pump Yellow - Clear Total Volume Dosed
    disabled_by_default: true
    icon: mdi:backspace
    id: dose_clear_yellow
    on_press:
      - ezo_pmp.clear_total_volume_dosed:
          id: ezo_pump_yellow
    web_server:
      sorting_group_id: sorting_group_pump_yellow

  # Calibrate
  - platform: template
    name: Pump Yellow - Set Calibration Volume
    icon: mdi:tape-measure
    id: dose_calibrate_volume_yellow
    on_press:
      - ezo_pmp.set_calibration_volume:
          id: ezo_pump_yellow
          volume: !lambda |-
            return id(volume_yellow).state;
    web_server:
      sorting_group_id: sorting_group_pump_yellow
  - platform: template
    name: Pump Yellow - Clear Calibration Volume
    disabled_by_default: true
    icon: mdi:cancel
    id: dose_calibrate_volume_clear_yellow
    on_press:
      - ezo_pmp.clear_calibration:
          id: ezo_pump_yellow
    web_server:
      sorting_group_id: sorting_group_pump_yellow
